ffsoup/looplauncher/looplaunch-layout-2.graffle/image1.png

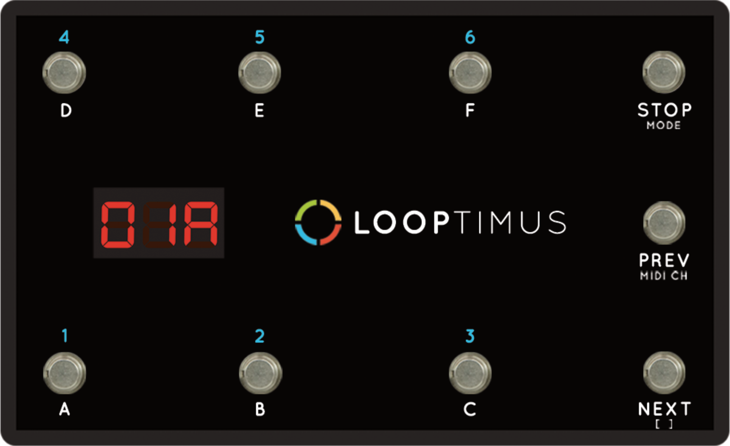
looplaunch-layout-2.graffle/image1.png
